lindseyr23/GuitarHero430/board2/PlaySong.h

/*
 * PlaySong.h
 *
 *  Created on: Apr 11, 2024
 *      Author: linds
 */

#ifndef PLAYSONG_H_
#define PLAYSONG_H_

void PlaySong(int a);
void MusicInit(void);
void StopSong(void);
void WinEffect(void);
void LossEffect(void);

#endif /* PLAYSONG_H_ */
